wwwcont/mpei-mps-kp/А-09-23/3 Друговская Е.М./СХЕМА-1/perechen.pdf

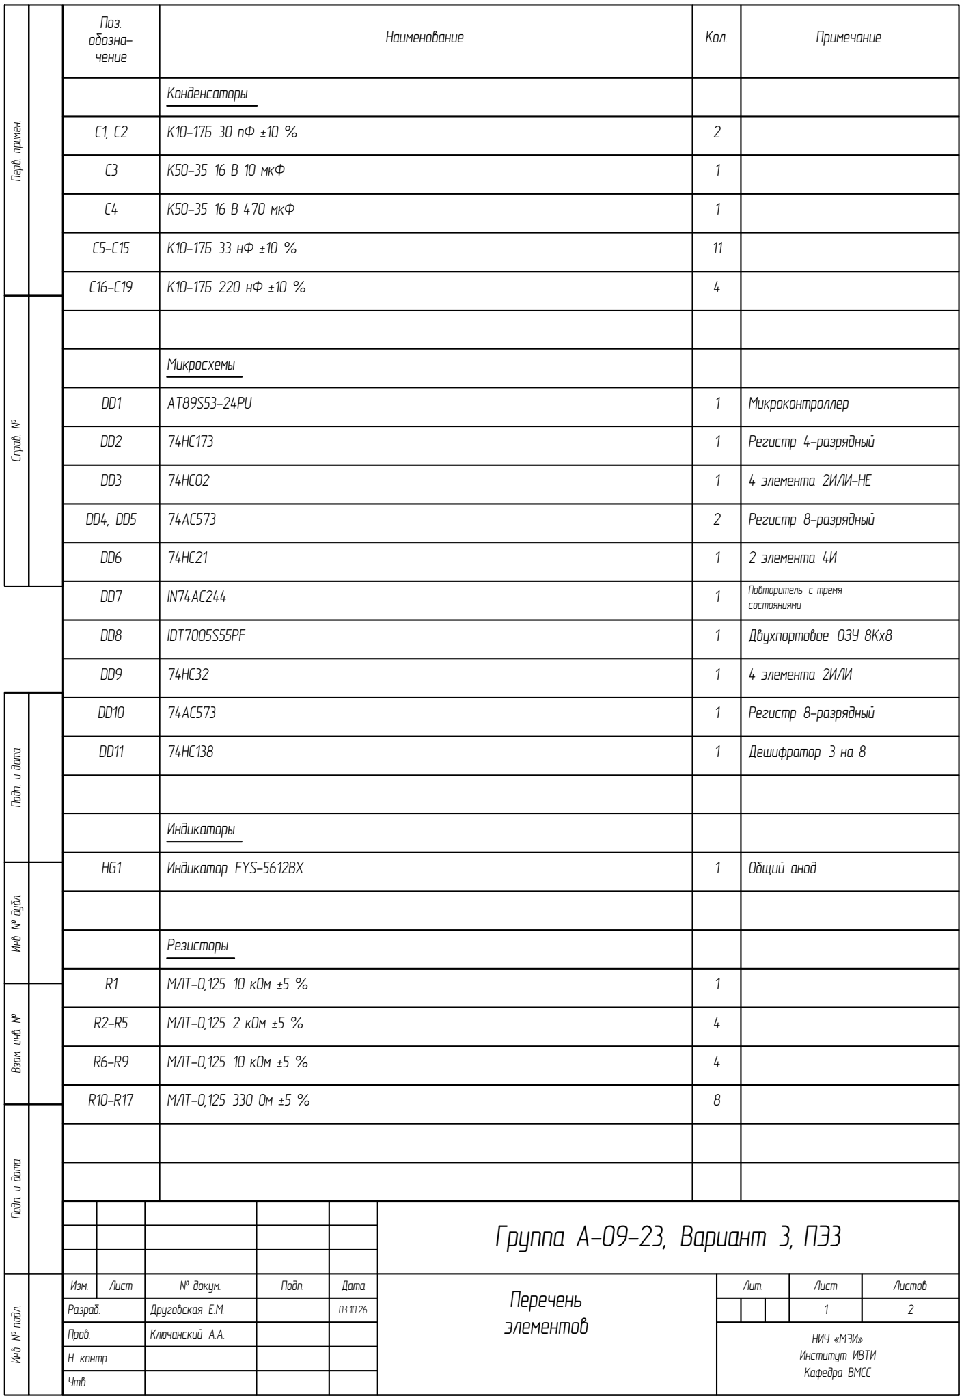
[picture p52: figure]
Изм.; Лист; № докум.; Подп.; Дата; Разраб.; Пров.; Н. контр.; Утв.; Друговская Е.М.; Перечень элементов; Лит.; Листов; НИУ «МЭИ» Институт ИВТИ; Микроконтроллер; IDT7005S55PF; Общий анод; МЛТ-0,125 330 Ом ±5 %; Резисторы; МЛТ-0,125 2 кОм ±5 %; МЛТ-0,125 10 кОм ±5 %; Индикатор FYS-5612BX; Индикаторы; Поз.; Двухпортовое ОЗУ 8Кx8; состояниями 1; 2 элемента 4И; Кол.; Примечание; 4 элемента 2ИЛИ; Наименование; Конденсаторы; обозна- чение; Регистр 8-разрядный; 4 элемента 2ИЛИ-НЕ; Регистр 4-разрядный; Микросхемы; К50-35 16 В 10 мкФ; К50-35 16 В 470 мкФ; Дешифратор 3 на 8; Повторитель с тремя

Ключанский А.А. | 03.10.26 | Группа А-09-23, Вариант 3, ПЭ3

Кафедра ВМСС Инв. № подл. Подп. и дата Взам. инв.

№ Инв. № дубл. Подп. и дата Перв. примен. Справ.

Изм. | Лист | № докум. | Подп. | Дата | Группа А-09-23, Вариант 3, ПЭ3

Лист

2 Инв. № подл. Подп. и дата Взам. инв.

№ Инв. № дубл. Подп. и дата

Диод КД521А

XS1

VD1–VD3

Диоды

Разъёмы

3

Розетка PBS-23

ZQ1 | 1

Резонаторы

Резонатор кварцевый HC-49S 12 МГц

обозна- | Наименование | Кол. | Примечание
чение
1 | 23 конт.
SB1–SB12 | Кнопка DTSM-62N-V | 12
| Кнопки

Поз.
