wwwcont/mpei-mps-kp/А-12-23/14 Студентов С.С./СХЕМА-1/perechen.pdf

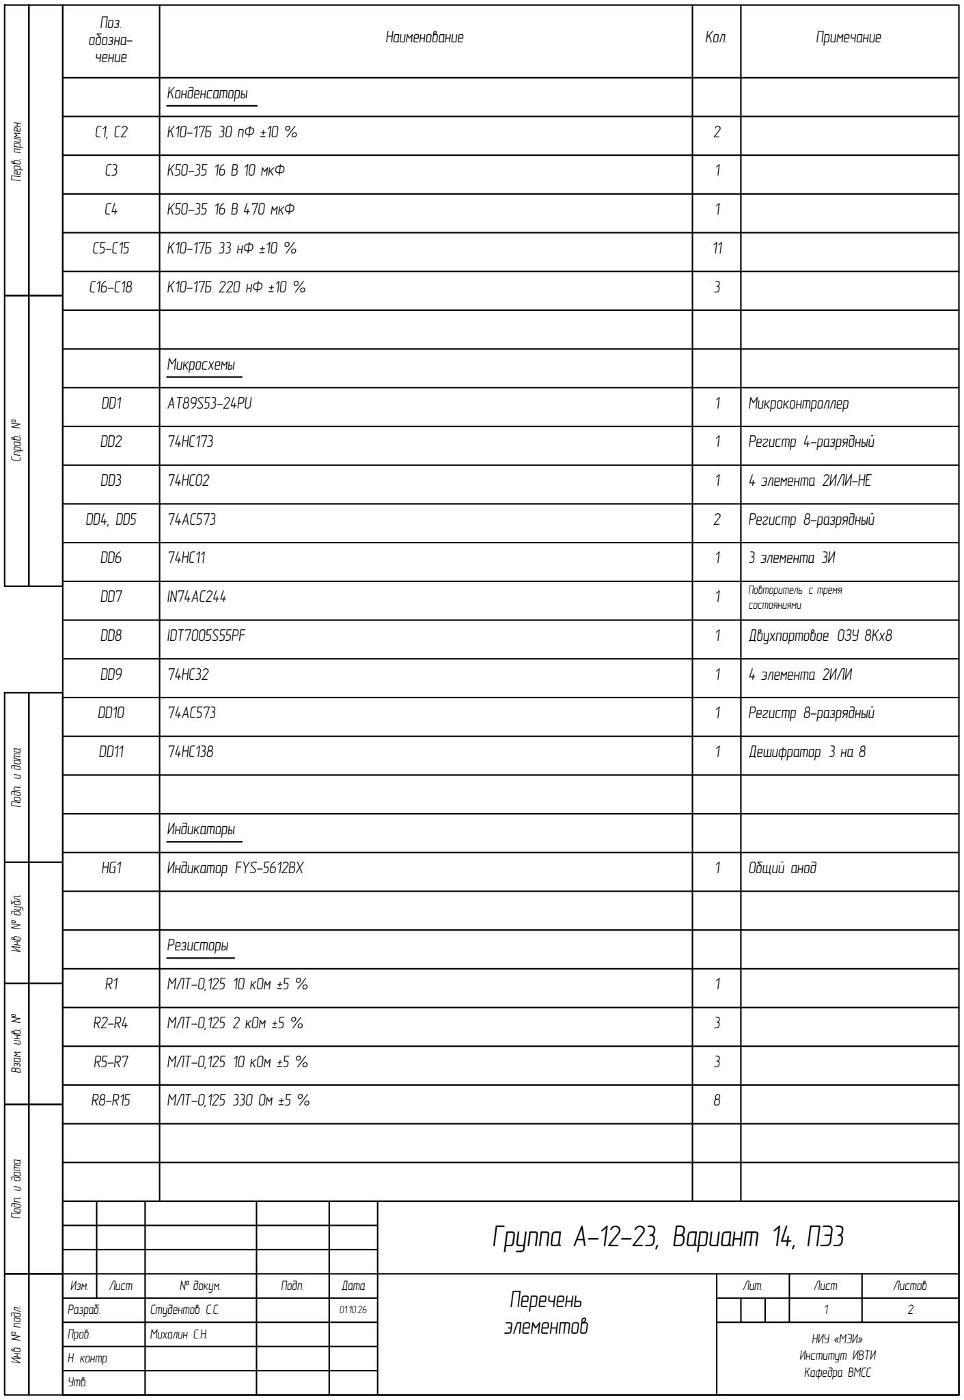
[picture p53: figure]
Изм.; Лист; № докум.; Подп.; Дата; Разраб.; Пров.; Н. контр.; Утв.; Студентов С.С.; Перечень элементов; Лит.; Листов; НИУ «МЭИ» Институт ИВТИ; Микроконтроллер; IDT7005S55PF; Общий анод; МЛТ-0,125 330 Ом ±5 %; Резисторы; МЛТ-0,125 2 кОм ±5 %; МЛТ-0,125 10 кОм ±5 %; Индикатор FYS-5612BX; Индикаторы; Поз.; Двухпортовое ОЗУ 8Кx8; состояниями 1; 3 элемента 3И; Кол.; Примечание; 4 элемента 2ИЛИ; Наименование; Конденсаторы; обозна- чение; Регистр 8-разрядный; 4 элемента 2ИЛИ-НЕ; Регистр 4-разрядный; Микросхемы; К50-35 16 В 10 мкФ; К50-35 16 В 470 мкФ; Дешифратор 3 на 8; Повторитель с тремя

Михалин С.Н. | 01.10.26 | Группа А-12-23, Вариант 14, ПЭ3

Кафедра ВМСС Инв. № подл. Подп. и дата Взам. инв.

№ Инв. № дубл. Подп. и дата Перв. примен. Справ.

Изм. | Лист | № докум. | Подп. | Дата | Группа А-12-23, Вариант 14, ПЭ3

Лист

2 Инв. № подл. Подп. и дата Взам. инв.

№ Инв. № дубл. Подп. и дата

XS1

XS3

XS2 | Розетка PBS-10
| Розетка PBS-11

1

Розетка PBS-2 | 2 конт.

Резонатор кварцевый HC-49S 12 МГц

1

Резонаторы

ZQ1

Наименование

Кнопки

SB1–SB12 | Кнопка DTSM-62N-V | 12
VD1–VD4 | Диод КД521А | 4

чение

обозна-

11 конт.

Кол. | Примечание

Поз.

Диоды

Разъёмы

10 конт.

1

1
