wwwcont/mpei-mps-kp/students/a06_groshev_av/pz/pz1.md

<!-- Текст студента для ПЗ1. Каждый раздел начинается строкой «## ид — название»: ид не менять.
     Строки «> ✍ …» — подсказки, в документ не попадают. Пиши под подсказкой обычными абзацами;
     markdown можно: **жирный**, *курсив*, списки через «- ». Пустой раздел → в документе жёлтое «ДОПИШИ».
     Файл можно пересоздать (make pz-init): написанный текст сохранится. -->

## p1.intro — Введение: своими словами
> ✍ одним абзацем — что делает твоя система и чем вариант отличается (клавиатура, индикатор, сигналы Y). Можно удалить подсказку, если введение устраивает.

Проектируемая система на AT89S53 собирает отсчёты X2, которые присылает внешнее устройство, в кольцевой буфер на двухпортовом ОЗУ IDT7005, а по ним и по числу X1, набранному оператором, вырабатывает выходной код Y2 = (7 + X1 + X2) mod 256 со стробом на P1.2. В моём варианте (А-06, M = 1) клавиатура 3×4 — три столбца и четыре строки, нажатие сообщается прерыванием INT0; введённая цифра выводится на семисегментный индикатор с общим катодом и гаснет через T3 = 2150 мс. Клавиша «Тест» запускает строб Y1 длительностью 176 мс на выводе P1.1, а буфер рассчитан на 1210 байт (адреса 2000h–24B9h). Все внешние устройства выбираются дешифратором 74HC138 по старшим линиям адреса A13–A15, пока CS_EN = P3.4 равен 1.

## p1.buffer — Механизм обмена через буфер
> ✍ опиши своими словами, как внешнее устройство записывает X2 и как МК читает буфер (кто выставляет адрес, какой строб, какое прерывание, кто двигает «голову» и «хвост»). 3–5 предложений.

Порты IDT7005 в моей схеме разделены между двумя хозяевами. Правый порт целиком выведен на отдельный разъём доступа к буферу: внешнее устройство само выставляет адрес A0R–A12R, данные I/O0R–I/O7R и строб на R/WR (CER постоянно на земле, OER — на +5 В) и записывает очередной отсчёт X2 в ячейку обмена 3FFFh, которая лежит за пределами кольца 2000h–24B9h. Тот же строб заведён на INT1 (P3.3): прерывание срабатывает по спаду, но ОЗУ фиксирует байт только по фронту, поэтому обработчик сначала дожидается, пока P3.3 вернётся в 1, и лишь затем читает 3FFFh. Левый порт полностью принадлежит МК — адрес A0–A12, данные D0–D7, CE от выхода Y1 дешифратора, OE от RD, R/W от WR, — так что через него программа и забирает байт из ячейки обмена, и пишет его в кольцо командой movx @DPTR,A по адресу «головы». Указатели «голова» и «хвост», а также флаги пустоты и переполнения хранятся во внутреннем ОЗУ и меняются только программой: «голову» сдвигает процедура записи, вызванная из обработчика INT1, «хвост» — процедура чтения в основном цикле. Прочитанный по «хвосту» отсчёт основная программа использует для расчёта Y2 = (7 + X1 + X2) mod 256 и выдаёт его со стробом на P1.2.

## p1.timing — Вывод по временам IDT7005
> ✍ свой вывод по сравнению времён (2–4 предложения) (необязательно: без текста в документ идёт пересказ схемы)
