wwwcont/mpei-mps-kp/students/a06_groshev_av/pz/pz2.md

<!-- Текст студента для ПЗ2. Каждый раздел начинается строкой «## ид — название»: ид не менять.
     Строки «> ✍ …» — подсказки, в документ не попадают. Пиши под подсказкой обычными абзацами;
     markdown можно: **жирный**, *курсив*, списки через «- ». Пустой раздел → в документе жёлтое «ДОПИШИ».
     Файл можно пересоздать (make pz-init): написанный текст сохранится. -->

## p2.ide — Среда разработки и компилятор
> ✍ если работали в другой среде — впишите свою (название и версия, например «MCU 8051 IDE 1.4.9») (необязательно: без текста в документ идёт пересказ схемы)

## p2.alg — Алгоритм программы в целом
> ✍ опиши основной цикл: что делается после сброса (инициализация), что крутится в основном цикле и какие действия выполняются в прерываниях (клавиатура — INT0, X2 — INT1, таймеры). 1–2 абзаца, со ссылками на рисунки ниже.

После сброса МК выполняет инициализацию (рисунок 1): ставит стек на 07h, разрешает дешифратор адреса (CS_EN = 1), переводит стробы Y1 и Y2 в пассивную единицу, опускает все столбцы клавиатуры и гасит индикатор, объявляет буфер пустым, настраивает Timer0 и Timer1 в режим 1, а INT0 и INT1 — на срабатывание по спаду, и только после этого разрешает прерывания. Основная программа (рисунок 2) в цикле смотрит, есть ли что выдавать: если X1 ≠ 0, в буфере есть отсчёт и предыдущий строб Y2 уже закончился, она читает отсчёт из «хвоста» и выдаёт Y2 = (7 + X1 + X2) mod 256 со стробом.

Всё, что связано со временем и с внешними событиями, сделано в прерываниях. INT0 приходит от клавиатуры: обработчик опрашивает матрицу (рисунок 3) и по коду клавиши меняет X1, запускает строб Y1 или очищает буфер (рисунок 4). INT1 — строб внешнего устройства, которым оно уже записало X2 в ячейку обмена 3FFFh через правый порт: обработчик ждёт, пока строб закончится, забирает байт из этой ячейки и кладёт его в кольцо по адресу «головы» (рисунки 5 и 6). Timer0 тикает каждые 2 мс и отсчитывает длительность строба Y1 и время индикации T3 (рисунок 10), Timer1 одним интервалом отмеряет строб Y2 1536 мкс и поднимает его (рисунок 13). Благодаря этому ни одна процедура не ждёт в цикле, и основная программа всегда готова обработать следующий отсчёт.

## flow.01-init — Пояснение к рисунку 1
> ✍ своё пояснение к рисунку 1 («Инициализация МПС и основная программа»): что делает алгоритм по шагам и почему так (3–6 предложений) (необязательно: без текста в документ идёт пересказ схемы)

## flow.02-main — Пояснение к рисунку 2
> ✍ своё пояснение к рисунку 2 («Основной цикл программы»): что делает алгоритм по шагам и почему так (3–6 предложений) (необязательно: без текста в документ идёт пересказ схемы)

## flow.03-kbscan — Пояснение к рисунку 3
> ✍ своё пояснение к рисунку 3 («Опрос клавиатуры (обработчик INT0)»): что делает алгоритм по шагам и почему так (3–6 предложений) (необязательно: без текста в документ идёт пересказ схемы)

Процедура KbScan по очереди опускает в 0 один из трёх столбцов и читает четыре строки. Старшие биты прочитанного байта не подключены, поэтому они отбрасываются маской, а оставшиеся биты инвертируются, чтобы замкнутая строка давала 1. Каждая найденная единица увеличивает счётчик нажатий, а индекс клавиши считается как номер столбца плюс три на каждую строку вниз — это сразу номер элемента в таблице KeyTab. После опроса все столбцы снова опускаются, иначе следующее нажатие не вызовет INT0, и сбрасывается IE0, который успел установиться, пока линия дёргалась при переборе столбцов. Код из таблицы возвращается, только если нажата ровно одна клавиша; иначе возвращается FFh.

## flow.04-keys — Пояснение к рисунку 4
> ✍ своё пояснение к рисунку 4 («Обработчик прерывания INT0: реакция на клавишу»): что делает алгоритм по шагам и почему так (3–6 предложений) (необязательно: без текста в документ идёт пересказ схемы)

## flow.05-bufwrite — Пояснение к рисунку 5
> ✍ своё пояснение к рисунку 5 («Запись отсчёта в кольцевой буфер»): что делает алгоритм по шагам и почему так (3–6 предложений) (необязательно: без текста в документ идёт пересказ схемы)

BufWrite сначала проверяет, полон ли буфер: это случай, когда буфер не пуст, а «голова» совпала с «хвостом» по обоим байтам адреса. Тогда самый старый отсчёт приносится в жертву — «хвост» сдвигается на одну ячейку, и ставится флаг переполнения. Затем отсчёт записывается по адресу «головы», «голова» переходит к следующей ячейке через общую подпрограмму NextCell (после 24B9h она возвращается на 2000h), а флаг пустоты сбрасывается. Так в буфере всегда помещается V = 1210 отсчётов, и при переполнении теряются самые давние данные, а не только что пришедшие.

## flow.05a-x2isr — Пояснение к рисунку 6
> ✍ своё пояснение к рисунку 6 («Обработчик прерывания INT1: приём отсчёта X2 от внешнего устройства»): что делает алгоритм по шагам и почему так (3–6 предложений) (необязательно: без текста в документ идёт пересказ схемы)

К моменту входа в обработчик внешнее устройство уже выставило отсчёт на правый порт IDT7005 и держит строб в нуле, но сама запись в ячейку обмена 3FFFh завершается только по фронту строба. Поэтому после сохранения A, PSW и DPTR обработчик крутится на проверке P3.3 и выходит из ожидания, когда строб вернулся в 1. Затем по адресу 3FFFh командой movx A,@DPTR через левый порт читается принятый байт и передаётся в BufWrite, которая кладёт его в кольцо и сдвигает «голову». В конце регистры восстанавливаются в обратном порядке. Ожидание короткое — оно длится не дольше самого строба, — а без него МК мог бы прочитать из ячейки обмена ещё прошлый отсчёт.

## flow.06-bufread — Пояснение к рисунку 7
> ✍ своё пояснение к рисунку 7 («Чтение отсчёта из кольцевого буфера»): что делает алгоритм по шагам и почему так (3–6 предложений) (необязательно: без текста в документ идёт пересказ схемы)

## flow.07-bufclear — Пояснение к рисунку 8
> ✍ своё пояснение к рисунку 8 («Очистка кольцевого буфера (клавиша «Сброс»)»): что делает алгоритм по шагам и почему так (3–6 предложений) (необязательно: без текста в документ идёт пересказ схемы)

## flow.08-show — Пояснение к рисунку 9
> ✍ своё пояснение к рисунку 9 («Вывод символа на индикатор»): что делает алгоритм по шагам и почему так (3–6 предложений) (необязательно: без текста в документ идёт пересказ схемы)

## flow.09-t0 — Пояснение к рисунку 10
> ✍ своё пояснение к рисунку 10 («Обработчик прерывания Timer0: отсчёт T1 и T3»): что делает алгоритм по шагам и почему так (3–6 предложений) (необязательно: без текста в документ идёт пересказ схемы)

Timer0 работает в 16-разрядном режиме и переполняется каждые 2 мс. В обработчике таймер на несколько тактов останавливается, и к тому, что он успел насчитать после переполнения, прибавляется F830h плюс семь тактов остановки — так задержка входа в прерывание не накапливается, и за 88 тиков строб получается 176 мс без заметной ошибки. После перезапуска уменьшается счётчик тиков; когда он доходит до нуля, таймер останавливается и строб Y1 поднимается в 1. A и PSW сохраняются в стеке, потому что прерывание может прийти в любом месте основной программы.

## flow.10-y1 — Пояснение к рисунку 11
> ✍ своё пояснение к рисунку 11 («Начало строба Y1»): что делает алгоритм по шагам и почему так (3–6 предложений) (необязательно: без текста в документ идёт пересказ схемы)

Y1Start не ждёт окончания строба, а только запускает его. Сначала Timer0 останавливается, чтобы повторное нажатие «Тест» начинало отсчёт заново, затем в таймер загружается первый тик 2 мс, а счётчик тиков ставится на 88. После этого вывод P1.1 опускается в 0 и таймер запускается; дальше длительность отсчитывает обработчик Timer0, а процедура сразу возвращается.

## flow.11-y2 — Пояснение к рисунку 12
> ✍ своё пояснение к рисунку 12 («Расчёт и выдача сигнала Y2»): что делает алгоритм по шагам и почему так (3–6 предложений) (необязательно: без текста в документ идёт пересказ схемы)

## flow.12-t1 — Пояснение к рисунку 13
> ✍ своё пояснение к рисунку 13 («Обработчик прерывания Timer1: конец строба Y2»): что делает алгоритм по шагам и почему так (3–6 предложений) (необязательно: без текста в документ идёт пересказ схемы)

## p2.errors — Коды ошибок
> ✍ проверь таблицу кодов ошибок выше: оставь те, что обрабатывает твоя программа, и одним-двумя предложениями опиши реакцию на ошибку (или напиши «таблица соответствует программе»).

Таблица описывает реакцию системы в целом. В моих программах ошибки «1.» и «2.» процедура опроса KbScan не различает — в обоих случаях она возвращает FFh, и обработчик клавиш выводит код ошибки; признаком ошибки «3.» служит флаг переполнения, который ставит BufWrite, когда новый отсчёт затирает непрочитанный, а «4.» относится к повторному нажатию «Тест» во время строба Y1 (в Y1Start такой вызов просто перезапускает отсчёт T1). Ошибка только показывается на индикаторе с точкой dp; указатели буфера, X1 и выходы Y1, Y2 при этом не меняются.
