wwwcont/mpei-mps-kp/students/a08_laptashkin_vi/pz/pz1.md

<!-- Текст студента для ПЗ1. Каждый раздел начинается строкой «## ид — название»: ид не менять.
     Строки «> ✍ …» — подсказки, в документ не попадают. Пиши под подсказкой обычными абзацами;
     markdown можно: **жирный**, *курсив*, списки через «- ». Пустой раздел → в документе жёлтое «ДОПИШИ».
     Файл можно пересоздать (make pz-init): написанный текст сохранится. -->

## p1.intro — Введение: своими словами
> ✍ одним абзацем — что делает твоя система и чем вариант отличается (клавиатура, индикатор, сигналы Y). Можно удалить подсказку, если введение устраивает.

В работе проектируется аппаратная часть микропроцессорной системы на AT89S53 для варианта 12 группы А-08. Система собирает отсчёты сигнала X2 от внешнего устройства в кольцевой буфер на 1528 байт (двухпортовое ОЗУ IDT7005, ячейки 6000h–65F7h), принимает команды и число X1 с клавиатуры 4×3, показывает символ на семисегментном индикаторе с общим анодом и формирует выходные сигналы: строб Y1 длительностью 298 мс на выводе P1.5 и байт Y2 = (20 + X1 + X2) mod 256, который заносится в отдельный регистр и сопровождается стробом 2068 мкс на P1.6. Особенность задания этого года — все внешние устройства выбираются через дешифратор 74HC138 по старшим разрядам адреса A13–A15 (у меня буфер — выход Y3, регистр Y2 — Y4, индикатор — Y5, клавиатура — Y6), а сам дешифратор включается линией CS_EN = P3.4.

## p1.buffer — Механизм обмена через буфер
> ✍ опиши своими словами, как внешнее устройство записывает X2 и как МК читает буфер (кто выставляет адрес, какой строб, какое прерывание, кто двигает «голову» и «хвост»). 3–5 предложений.

У IDT7005 два полностью независимых порта, и каждый подключён к своему хозяину. Левый порт целиком принадлежит микроконтроллеру: на него идут адрес A0–A12 с шины, данные D0–D7, выбор CS_buf (выход Y3 дешифратора), OE от RD и R/W от WR, поэтому через него МК и записывает отсчёты в кольцо 6000h–65F7h, и читает их обратно. Правый порт выведен на отдельный разъём: внешнее устройство само выставляет адрес 7FFFh (ячейка обмена за пределами кольца) и байт X2, а своим стробом X2 на R/WR записывает его в ОЗУ; CER у правого порта постоянно на земле, OER — на +5 В. Тот же строб заведён на INT1, и прерывание приходит по его спаду, тогда как байт фиксируется в ячейке только по фронту, поэтому обработчик сначала ждёт, пока P3.3 вернётся в 1, и лишь потом читает ячейку 7FFFh через левый порт. Прочитанный отсчёт МК кладёт по адресу «головы» процедурой записи в буфер, сдвигает «голову» и ведёт флаги пустоты и переполнения — внешнее устройство об указателях ничего не знает. Когда отсчёт нужен для расчёта Y2, МК читает ячейку «хвоста» командой movx A, @DPTR, сдвигает «хвост» (на границе 65F7h оба указателя заворачиваются на 6000h) и пересчитанный байт заносит в регистр Y2.

## p1.timing — Вывод по временам IDT7005
> ✍ свой вывод по сравнению времён (2–4 предложения) (необязательно: без текста в документ идёт пересказ схемы)

Из таблицы видно, что самое жёсткое требование ОЗУ — выдать данные не позже 55 нс после установки адреса, а МК при кварце 12 МГц ждёт их почти 500 нс, то есть микросхема успевает с большим запасом. При записи в кольцо импульс WR длится не меньше 400 нс против нужных IDT7005 40 нс, а данные на P0 держатся всё это время, так что запись левым портом тоже проходит надёжно. Правый порт от МК не зависит: его времена должно выдерживать внешнее устройство на разъёме. Значит, буфер можно подключать прямо к шине P0/P2 без дополнительных задержек и согласующих элементов.
