wwwcont/mpei-mps-kp/students/a08_laptashkin_vi/pz/pz2.md

<!-- Текст студента для ПЗ2. Каждый раздел начинается строкой «## ид — название»: ид не менять.
     Строки «> ✍ …» — подсказки, в документ не попадают. Пиши под подсказкой обычными абзацами;
     markdown можно: **жирный**, *курсив*, списки через «- ». Пустой раздел → в документе жёлтое «ДОПИШИ».
     Файл можно пересоздать (make pz-init): написанный текст сохранится. -->

## p2.ide — Среда разработки и компилятор
> ✍ если работали в другой среде — впишите свою (название и версия, например «MCU 8051 IDE 1.4.9») (необязательно: без текста в документ идёт пересказ схемы)

## p2.alg — Алгоритм программы в целом
> ✍ опиши основной цикл: что делается после сброса (инициализация), что крутится в основном цикле и какие действия выполняются в прерываниях (клавиатура — INT0, X2 — INT1, таймеры). 1–2 абзаца, со ссылками на рисунки ниже.

После сброса МПС выполняет инициализацию (рисунок 3.1): ставит стек на 07h, включает дешифратор адреса линией CS_EN, опускает все столбцы клавиатуры, гасит индикатор, задаёт режимы таймеров и разрешает прерывания. Дальше всю срочную работу делают обработчики: INT0 срабатывает по нажатию клавиши и вызывает опрос матрицы, INT1 по стробу X2 дожидается конца строба, забирает из ячейки обмена отсчёт, который внешнее устройство записало туда правым портом IDT7005, и кладёт его в кольцевой буфер, Timer0 отсчитывает длительности T1 (строб Y1) и T3 (время показа символа), а Timer1 — длительность строба Y2.

Основной цикл (рисунок 3.2) только следит за условием выдачи Y2: если X1 ≠ 0, в буфере есть отсчёты и предыдущий строб Y2 закончился, он забирает отсчёт из буфера, считает Y2 = (20 + X1 + X2) mod 256 и выдаёт его со стробом; при X1 = 0 в регистр один раз записывается ноль. Три программы для робота — это отдельные куски этой системы: обработчик клавиатуры (рисунок 3.3), чтение из буфера (рисунок 3.7) и вывод символа с гашением по T3 (рисунки 3.9 и 3.10); в них сделана только своя часть инициализации, остальное время МК стоит на команде jmp $.

## flow.01-init — Пояснение к рисунку 3.1
> ✍ своё пояснение к рисунку 3.1 («Инициализация МПС и основная программа»): что делает алгоритм по шагам и почему так (3–6 предложений) (необязательно: без текста в документ идёт пересказ схемы)

Сначала задаётся SP = 07h, чтобы стек лежал сразу за банком регистров 0, и ставится CS_EN = 1 — без этого дешифратор 74HC138 не выдаст ни одного CS и команды movx никуда не попадут. Затем переменные получают начальные значения: буфер пуст (голова = хвост = 6000h, F_EMPTY = 1), X1 = 0, стробы Y1 и Y2 в единице. В регистр столбцов пишется 0, чтобы любое нажатие сразу опустило строку и дало спад на INT0, а индикатор гасится кодом FFh. Последними настраиваются таймеры и разрешаются прерывания: если разрешить их раньше, обработчик мог бы застать недонастроенные переменные.

## flow.02-main — Пояснение к рисунку 3.2
> ✍ своё пояснение к рисунку 3.2 («Основной цикл программы»): что делает алгоритм по шагам и почему так (3–6 предложений) (необязательно: без текста в документ идёт пересказ схемы)

## flow.03-kbscan — Пояснение к рисунку 3.3
> ✍ своё пояснение к рисунку 3.3 («Опрос клавиатуры (обработчик INT0)»): что делает алгоритм по шагам и почему так (3–6 предложений) (необязательно: без текста в документ идёт пересказ схемы)

Опрос идёт по столбцам: маска с одним нулём записывается в регистр столбцов, и из ячейки клавиатуры читаются три младших бита — состояние строк, старшие биты шины отбрасываются. Внутри столбца строки перебираются сдвигом через перенос, номер клавиши при переходе на строку ниже увеличивается на 4 (число столбцов). Я не останавливаюсь на первом найденном контакте, а считаю все замыкания: только если за весь опрос нашлось ровно одно, номер клавиши переводится в код по таблице KbCodes, иначе (помеха или две клавиши сразу) возвращается FFh. В конце все столбцы снова опускаются в 0, а IE0 сбрасывается — пока перебирались столбцы, линия INT0 дёргалась, и без сброса обработчик вызвался бы ещё раз.

## flow.04-keys — Пояснение к рисунку 3.4
> ✍ своё пояснение к рисунку 3.4 («Обработчик прерывания INT0: реакция на клавишу»): что делает алгоритм по шагам и почему так (3–6 предложений) (необязательно: без текста в документ идёт пересказ схемы)

## flow.05-bufwrite — Пояснение к рисунку 3.5
> ✍ своё пояснение к рисунку 3.5 («Запись отсчёта в кольцевой буфер»): что делает алгоритм по шагам и почему так (3–6 предложений) (необязательно: без текста в документ идёт пересказ схемы)

## flow.05a-x2isr — Пояснение к рисунку 3.6
> ✍ своё пояснение к рисунку 3.6 («Обработчик прерывания INT1: приём отсчёта X2 от внешнего устройства»): что делает алгоритм по шагам и почему так (3–6 предложений) (необязательно: без текста в документ идёт пересказ схемы)

К моменту прерывания отсчёт X2 уже пишется внешним устройством через правый порт IDT7005 в ячейку обмена 7FFFh — МК в этой записи не участвует. Обработчик сохраняет A, PSW и DPTR, потому что вызывается посреди любой другой работы. Затем он крутится на проверке P3.3: INT1 настроен на спад строба, а в ОЗУ байт защёлкивается только по фронту, и если читать сразу, можно получить старое содержимое ячейки. Когда строб закончился, ячейка 7FFFh читается левым портом командой movx A, @DPTR, и отсчёт передаётся процедуре записи в кольцо (рисунок 3.5), которая сама сдвигает «голову» и ставит флаги. В конце регистры восстанавливаются в обратном порядке.

## flow.06-bufread — Пояснение к рисунку 3.7
> ✍ своё пояснение к рисунку 3.7 («Чтение отсчёта из кольцевого буфера»): что делает алгоритм по шагам и почему так (3–6 предложений) (необязательно: без текста в документ идёт пересказ схемы)

Сначала проверяется флаг пустоты: если читать нечего, процедура сразу возвращает 0 и не трогает ни указатели, ни флаги. Иначе адрес «хвоста» загружается в DPTR, байт читается через левый порт IDT7005 и откладывается в B, потому что аккумулятор нужен для сравнений. «Хвост» увеличивается на единицу, и если он дошёл до BUF_END = 65F8h (сравниваются оба байта адреса), то возвращается на начало 6000h. После чтения одна ячейка заведомо свободна, поэтому флаг переполнения сбрасывается, а если «хвост» догнал «голову», ставится флаг пустоты.

## flow.07-bufclear — Пояснение к рисунку 3.8
> ✍ своё пояснение к рисунку 3.8 («Очистка кольцевого буфера (клавиша «Сброс»)»): что делает алгоритм по шагам и почему так (3–6 предложений) (необязательно: без текста в документ идёт пересказ схемы)

## flow.08-show — Пояснение к рисунку 3.9
> ✍ своё пояснение к рисунку 3.9 («Вывод символа на индикатор»): что делает алгоритм по шагам и почему так (3–6 предложений) (необязательно: без текста в документ идёт пересказ схемы)

Процедура сначала останавливает Timer0 и сбрасывает TF0: если предыдущий символ ещё показывается, его отсчёт T3 прерывается и начинается заново. Код больше 10 означает «погасить» — в регистр индикатора сразу пишется FFh, и таймер не запускается. Для кодов 0–10 сегменты берутся из таблицы SegTab, составленной для общего катода, и инвертируются командой xrl A, #IND_OFF, так как у моего индикатора общий анод и сегмент горит при нуле. После записи символа задаётся счёт тиков T3 (1410 по 2 мс) и запускается Timer0; процедура возвращается сразу, ожидание идёт в прерываниях.

## flow.09-t0 — Пояснение к рисунку 3.10
> ✍ своё пояснение к рисунку 3.10 («Обработчик прерывания Timer0: отсчёт T1 и T3»): что делает алгоритм по шагам и почему так (3–6 предложений) (необязательно: без текста в документ идёт пересказ схемы)

Timer0 работает в режиме 2 (8 бит с автоперезагрузкой): переполнение приходит каждые 200 мкс, и перезагружать таймер программно не нужно, поэтому задержка входа в прерывание не копится в длительности. Десять переполнений образуют тик 2 мс, на каждом тике уменьшается двухбайтовый счётчик тиков (младший байт гоняется командой djnz, старший — после каждого его круга). Когда тики кончились, таймер останавливается и в зависимости от того, что отсчитывалось, либо снимается строб Y1, либо гасится индикатор. Команды djnz не меняют флаги, поэтому PSW сохранять не нужно, а A и DPTR кладутся в стек только в ветке гашения, где они реально используются; в программе 3 используется только ветка T3.

## flow.10-y1 — Пояснение к рисунку 3.11
> ✍ своё пояснение к рисунку 3.11 («Начало строба Y1»): что делает алгоритм по шагам и почему так (3–6 предложений) (необязательно: без текста в документ идёт пересказ схемы)

## flow.11-y2 — Пояснение к рисунку 3.12
> ✍ своё пояснение к рисунку 3.12 («Расчёт и выдача сигнала Y2»): что делает алгоритм по шагам и почему так (3–6 предложений) (необязательно: без текста в документ идёт пересказ схемы)

## flow.12-t1 — Пояснение к рисунку 3.13
> ✍ своё пояснение к рисунку 3.13 («Обработчик прерывания Timer1: конец строба Y2»): что делает алгоритм по шагам и почему так (3–6 предложений) (необязательно: без текста в документ идёт пересказ схемы)

## p2.errors — Коды ошибок
> ✍ проверь таблицу кодов ошибок выше: оставь те, что обрабатывает твоя программа, и одним-двумя предложениями опиши реакцию на ошибку (или напиши «таблица соответствует программе»).

Таблица описывает реакцию полной системы. В сданных программах из неё реализовано распознавание ошибок клавиатуры: если при опросе замкнуто больше одного контакта или прерывание пришло без нажатия, процедура KbScan возвращает FFh вместо кода клавиши, и вместо цифры на индикатор выводится код ошибки с горящей точкой. Оба случая дают в A одно и то же FFh; различить «1.» и «2.» можно по числу найденных замыканий (больше одного или ни одного), которое процедура считает во время опроса. Переполнение буфера («3.») отмечается флагом F_OVF, который снимает процедура чтения; «4.» выводится, если «Тест» нажат во время строба Y1. Индикация ошибки держится до нажатия любой клавиши, но не дольше T3.
