wwwcont/mpei-mps-kp/students/a09_drugovskaya_em/pz/pz1.md

<!-- Текст студента для ПЗ1. Каждый раздел начинается строкой «## ид — название»: ид не менять.
     Строки «> ✍ …» — подсказки, в документ не попадают. Пиши под подсказкой обычными абзацами;
     markdown можно: **жирный**, *курсив*, списки через «- ». Пустой раздел → в документе жёлтое «ДОПИШИ».
     Файл можно пересоздать (make pz-init): написанный текст сохранится. -->

## p1.intro — Введение: своими словами
> ✍ одним абзацем — что делает твоя система и чем вариант отличается (клавиатура, индикатор, сигналы Y). Можно удалить подсказку, если введение устраивает.

Разрабатываемая система собрана на микроконтроллере AT89S53: она принимает поток отсчётов X2 от внешнего устройства, накапливает их в кольцевом буфере на двухпортовом ОЗУ IDT7005 и по каждому отсчёту выдаёт результат Y2 = (12 + X1 + X2) mod 256 в выходной регистр со стробом. Число X1 оператор набирает на клавиатуре 3×4 (три столбца, четыре строки — нечётный вариант), введённый символ на время T3 = 2430 мс показывается на семисегментном индикаторе с общим анодом. Клавиша «Тест» запускает строб Y1 длительностью 215 мс на выводе P1.3, строб Y2 длительностью 1899 мкс выдаётся на P1.4. Внешние устройства выбираются дешифратором 74HC138 по старшим линиям адреса: буфер — выходом Y4, индикатор — Y5, регистр Y2 — Y6, клавиатура — Y7.

## p1.buffer — Механизм обмена через буфер
> ✍ опиши своими словами, как внешнее устройство записывает X2 и как МК читает буфер (кто выставляет адрес, какой строб, какое прерывание, кто двигает «голову» и «хвост»). 3–5 предложений.

Отсчёт X2 попадает в микроконтроллер в два этапа. Сначала внешнее устройство через отдельный разъём доступа к буферу само выставляет на правом порту IDT7005 адрес ячейки обмена 9FFFh (последняя ячейка окна буфера, вне кольца) и байт X2 и даёт строб записи — микроконтроллер в этом не участвует. Тот же строб заведён на вход INT1 (P3.3): прерывание срабатывает по спаду, а ОЗУ фиксирует байт по фронту, поэтому обработчик сначала дожидается, пока P3.3 вернётся в единицу, и только потом читает ячейку 9FFFh через левый порт. Прочитанный отсчёт процедура записи кладёт в кольцо 8000h–85F9h (1530 байт) по адресу «головы» и сдвигает её; если кольцо уже заполнено, вперёд уходит и «хвост», самый старый отсчёт теряется и ставится флаг переполнения. Основная программа забирает отсчёты по «хвосту» тем же левым портом и по ним вычисляет и выдаёт Y2. «Голова», «хвост» и флаги пустоты и переполнения хранятся во внутренней памяти микроконтроллера (44h–47h, биты 20h.3 и 21h.4), и меняет их только программа.

## p1.timing — Вывод по временам IDT7005
> ✍ свой вывод по сравнению времён (2–4 предложения) (необязательно: без текста в документ идёт пересказ схемы)

По таблице сравнения видно, что IDT7005 намного быстрее, чем требует шина AT89S53 при кварце 12 МГц: памяти нужно 55 нс от адреса до данных и 40 нс на импульс записи, а микроконтроллер отводит на это около 500 и 400 нс. Поэтому буфер подключается к шине напрямую, без тактов ожидания, а запас в сотни наносекунд с избытком покрывает задержки защёлки адреса и дешифратора.
