wwwcont/mpei-mps-kp/students/a09_drugovskaya_em/pz/pz2.md

<!-- Текст студента для ПЗ2. Каждый раздел начинается строкой «## ид — название»: ид не менять.
     Строки «> ✍ …» — подсказки, в документ не попадают. Пиши под подсказкой обычными абзацами;
     markdown можно: **жирный**, *курсив*, списки через «- ». Пустой раздел → в документе жёлтое «ДОПИШИ».
     Файл можно пересоздать (make pz-init): написанный текст сохранится. -->

## p2.ide — Среда разработки и компилятор
> ✍ если работали в другой среде — впишите свою (название и версия, например «MCU 8051 IDE 1.4.9») (необязательно: без текста в документ идёт пересказ схемы)

## p2.alg — Алгоритм программы в целом
> ✍ опиши основной цикл: что делается после сброса (инициализация), что крутится в основном цикле и какие действия выполняются в прерываниях (клавиатура — INT0, X2 — INT1, таймеры). 1–2 абзаца, со ссылками на рисунки ниже.

После сброса программа один раз проходит инициализацию (рисунок 1): указатель стека ставится на 07h, сигналом CS_EN = 1 включается дешифратор адреса, стробы Y1 и Y2 переводятся в пассивную единицу, все три столбца клавиатуры опускаются в ноль, индикатор гасится, буфер объявляется пустым (голова и хвост на 8000h, флаг пустоты взведён), оба таймера настраиваются в 16-разрядный режим и разрешаются прерывания. Основной цикл (рисунок 2) только следит за буфером: пока X1 не равно нулю и в буфере есть отсчёты, он берёт очередной отсчёт X2 по хвосту, считает Y2 = (12 + X1 + X2) mod 256 и выдаёт его со стробом; при X1 = 0 он один раз выдаёт нулевое Y2.

Всё, что приходит снаружи, обрабатывается в прерываниях. Нажатие клавиши даёт INT0: обработчик опрашивает матрицу 3×4 (рисунок 3) и по коду запоминает X1 и показывает цифру, запускает строб Y1 или очищает буфер (рисунок 4). Строб X2 от внешнего устройства приходит на INT1 по спаду; отсчёт к этому моменту ещё только записывается правым портом в ячейку обмена 9FFFh (ОЗУ фиксирует его по фронту строба), поэтому обработчик сначала ждёт, пока P3.3 вернётся в 1, затем читает ячейку левым портом и кладёт отсчёт в кольцо (рисунки 5 и 6). Длительности отсчитывают таймеры: Timer0 с тиком 5 мс заканчивает строб Y1 через 43 тика и гасит индикатор через 486 тиков (рисунок 10), Timer1 одной загрузкой отмеряет строб Y2 (рисунок 13).

## flow.01-init — Пояснение к рисунку 1
> ✍ своё пояснение к рисунку 1 («Инициализация МПС и основная программа»): что делает алгоритм по шагам и почему так (3–6 предложений) (необязательно: без текста в документ идёт пересказ схемы)

## flow.02-main — Пояснение к рисунку 2
> ✍ своё пояснение к рисунку 2 («Основной цикл программы»): что делает алгоритм по шагам и почему так (3–6 предложений) (необязательно: без текста в документ идёт пересказ схемы)

## flow.03-kbscan — Пояснение к рисунку 3
> ✍ своё пояснение к рисунку 3 («Опрос клавиатуры (обработчик INT0)»): что делает алгоритм по шагам и почему так (3–6 предложений) (необязательно: без текста в документ идёт пересказ схемы)

Процедура KbScan опускает в ноль по очереди один из трёх столбцов и каждый раз читает строки. Старшие биты прочитанного байта не подключены, поэтому они отбрасываются, а оставшиеся четыре инвертируются, чтобы единица означала замкнутую строку. Каждую замкнутую строку процедура считает и запоминает номер клавиши как «строка × 3 + столбец». После перебора все столбцы снова опускаются, иначе следующее нажатие не даст прерывания, и сбрасывается флаг IE0, который взвёлся, пока столбцы переключались. Если найдено ровно одно нажатие, номер переводится в код по таблице KeyTab, иначе возвращается FFh.

## flow.04-keys — Пояснение к рисунку 4
> ✍ своё пояснение к рисунку 4 («Обработчик прерывания INT0: реакция на клавишу»): что делает алгоритм по шагам и почему так (3–6 предложений) (необязательно: без текста в документ идёт пересказ схемы)

## flow.05-bufwrite — Пояснение к рисунку 5
> ✍ своё пояснение к рисунку 5 («Запись отсчёта в кольцевой буфер»): что делает алгоритм по шагам и почему так (3–6 предложений) (необязательно: без текста в документ идёт пересказ схемы)

Процедура BufWrite сначала проверяет, не заполнено ли кольцо: это случай, когда голова совпала с хвостом, а флаг пустоты сброшен. Тогда хвост сдвигается на одну ячейку вперёд, самый старый отсчёт пропадает и ставится флаг переполнения — то есть кольцо вмещает все 1530 отсчётов (политика V). Затем отсчёт записывается левым портом по адресу головы, голова сдвигается, флаг пустоты сбрасывается. Переход на следующую ячейку вынесен в отдельную процедуру PtrStep: она увеличивает адрес и после 85F9h возвращает его на 8000h, сравнивая оба байта.

## flow.05a-x2isr — Пояснение к рисунку 6
> ✍ своё пояснение к рисунку 6 («Обработчик прерывания INT1: приём отсчёта X2 от внешнего устройства»): что делает алгоритм по шагам и почему так (3–6 предложений) (необязательно: без текста в документ идёт пересказ схемы)

Обработчик INT1 вызывается по спаду строба X2, но правый порт IDT7005 запоминает байт только по его фронту, поэтому первым делом обработчик крутится, пока на P3.3 снова не появится единица. После этого в ячейке обмена 9FFFh гарантированно лежит новый отсчёт, и обработчик читает его левым портом командой movx. Прочитанный байт передаётся процедуре записи в кольцо (рисунок 5), которая сама ведёт голову, хвост и флаги. Регистры A, PSW и DPTR сохраняются в стеке, потому что прерывание может прийти в любой точке основной программы.

## flow.06-bufread — Пояснение к рисунку 7
> ✍ своё пояснение к рисунку 7 («Чтение отсчёта из кольцевого буфера»): что делает алгоритм по шагам и почему так (3–6 предложений) (необязательно: без текста в документ идёт пересказ схемы)

## flow.07-bufclear — Пояснение к рисунку 8
> ✍ своё пояснение к рисунку 8 («Очистка кольцевого буфера (клавиша «Сброс»)»): что делает алгоритм по шагам и почему так (3–6 предложений) (необязательно: без текста в документ идёт пересказ схемы)

## flow.08-show — Пояснение к рисунку 9
> ✍ своё пояснение к рисунку 9 («Вывод символа на индикатор»): что делает алгоритм по шагам и почему так (3–6 предложений) (необязательно: без текста в документ идёт пересказ схемы)

Процедура Show получает код символа в аккумуляторе. Коды 0–10 переводятся по таблице SegTab сразу в коды сегментов для индикатора с общим анодом (сегмент горит при нуле) и записываются в регистр индикатора. После этого отсчёт T3 начинается заново: Timer0 останавливается, счётчик тиков получает значение 486 (2430 мс по 5 мс), таймер загружается на первый тик и запускается — поэтому новый символ всегда горит полное T3. Для кодов 11 и больше индикатор сразу гасится, а таймер останавливается, так как ждать нечего.

## flow.09-t0 — Пояснение к рисунку 10
> ✍ своё пояснение к рисунку 10 («Обработчик прерывания Timer0: отсчёт T1 и T3»): что делает алгоритм по шагам и почему так (3–6 предложений) (необязательно: без текста в документ идёт пересказ схемы)

Таймер 0 работает в 16-разрядном режиме и сам не перезагружается, поэтому обработчик на каждом тике заново загружает его на 5 мс. К загружаемому значению прибавляется то, что таймер успел насчитать после переполнения, плюс семь циклов, пока он стоит, — так задержка входа в прерывание не накапливается за 486 тиков. Затем уменьшается 16-разрядный счётчик тиков, и когда он доходит до нуля, таймер останавливается и индикатор гаснет (в полной системе тот же таймер заканчивает и строб Y1).

## flow.10-y1 — Пояснение к рисунку 11
> ✍ своё пояснение к рисунку 11 («Начало строба Y1»): что делает алгоритм по шагам и почему так (3–6 предложений) (необязательно: без текста в документ идёт пересказ схемы)

## flow.11-y2 — Пояснение к рисунку 12
> ✍ своё пояснение к рисунку 12 («Расчёт и выдача сигнала Y2»): что делает алгоритм по шагам и почему так (3–6 предложений) (необязательно: без текста в документ идёт пересказ схемы)

## flow.12-t1 — Пояснение к рисунку 13
> ✍ своё пояснение к рисунку 13 («Обработчик прерывания Timer1: конец строба Y2»): что делает алгоритм по шагам и почему так (3–6 предложений) (необязательно: без текста в документ идёт пересказ схемы)

## p2.errors — Коды ошибок
> ✍ проверь таблицу кодов ошибок выше: оставь те, что обрабатывает твоя программа, и одним-двумя предложениями опиши реакцию на ошибку (или напиши «таблица соответствует программе»).

Таблица описывает реакцию полной системы. В написанных программах источники ошибок такие: процедура опроса клавиатуры возвращает FFh и при нескольких нажатых клавишах, и при отсутствии нажатия (в полной системе обработчик INT0 в ответ на FFh выводит код ошибки на индикатор, рисунок 4), а процедура записи в буфер при затирании непрочитанного отсчёта ставит флаг переполнения 21h.4 (код «3.»). Код «4.» относится к стробу Y1, который в трёх программах варианта не реализуется.
