wwwcont/mpei-mps-kp/students/ae21_sudbinin_na/pz/pz1.md

<!-- Текст студента для ПЗ1. Каждый раздел начинается строкой «## ид — название»: ид не менять.
     Строки «> ✍ …» — подсказки, в документ не попадают. Пиши под подсказкой обычными абзацами;
     markdown можно: **жирный**, *курсив*, списки через «- ». Пустой раздел → в документе жёлтое «ДОПИШИ».
     Файл можно пересоздать (make pz-init): написанный текст сохранится. -->

## p1.intro — Введение: своими словами
> ✍ одним абзацем — что делает твоя система и чем вариант отличается (клавиатура, индикатор, сигналы Y). Можно удалить подсказку, если введение устраивает.
Разрабатываемая система на микроконтроллере AT89S53 принимает от внешнего устройства поток восьмиразрядных отсчётов X2, складывает их в кольцевой буфер на двухпортовой памяти IDT7005, а с пульта получает цифру X1 и по ним выдаёт на выходной регистр сигнал Y2 = (21 + 11 + X1 + X2) mod 256 со стробом длительностью 1751 мкс на выводе P1.5. Кроме этого, клавишей «Тест» формируется строб Y1 на P1.4 длительностью 313 мс, а нажатый символ держится на индикаторе 2,745 с. Особенности моего варианта (Аэ-21, M = 11): клавиатура 3×4 (три столбца, четыре строки), индикатор с общим катодом, буфер на 1910 байт выбирается выходом Y7 дешифратора 74HC138, регистр Y2 — выходом Y2, индикатор — Y1, клавиатура — Y3.

## p1.buffer — Механизм обмена через буфер
> ✍ опиши своими словами, как внешнее устройство записывает X2 и как МК читает буфер (кто выставляет адрес, какой строб, какое прерывание, кто двигает «голову» и «хвост»). 3–5 предложений.
Порты IDT7005 у меня разделены: левый целиком подключён к микроконтроллеру (A0–A12, D0–D7, CE от выхода Y7 дешифратора, OE от RD, R/W от WR), а правый целиком выведен на отдельный разъём доступа к буферу, где адрес, данные и строб записи R/W выставляет само внешнее устройство (CE и OE правого порта постоянно активны). Очередной отсчёт X2 внешнее устройство записывает правым портом в ячейку обмена 0FFFFh, которая лежит вне кольца 0E000h–0E775h, и тот же строб записи приходит на вход INT1. Прерывание срабатывает по спаду строба, а память фиксирует байт только по его фронту, поэтому обработчик INT1 сначала ждёт, пока на P3.3 снова появится единица, и лишь потом читает ячейку обмена левым портом (movx A,@DPTR по RD). Прочитанный отсчёт обработчик передаёт процедуре записи, которая кладёт его в ячейку «головы», сдвигает «голову» (после 0E775h — на 0E000h) и снимает флаг пустоты; при заполненном кольце она же сдвигает «хвост», выбрасывая самый старый отсчёт, и ставит флаг переполнения. Указатели и флаги целиком ведёт МК: при расчёте Y2 процедура чтения берёт отсчёт из ячейки «хвоста» тем же левым портом и сдвигает «хвост», а результат уходит в регистр Y2.

## p1.timing — Вывод по временам IDT7005
> ✍ свой вывод по сравнению времён (2–4 предложения) (необязательно: без текста в документ идёт пересказ схемы)
