wwwcont/mpei-mps-kp/А-09-23/3 Друговская Е.М./СХЕМА-1/schematic.png

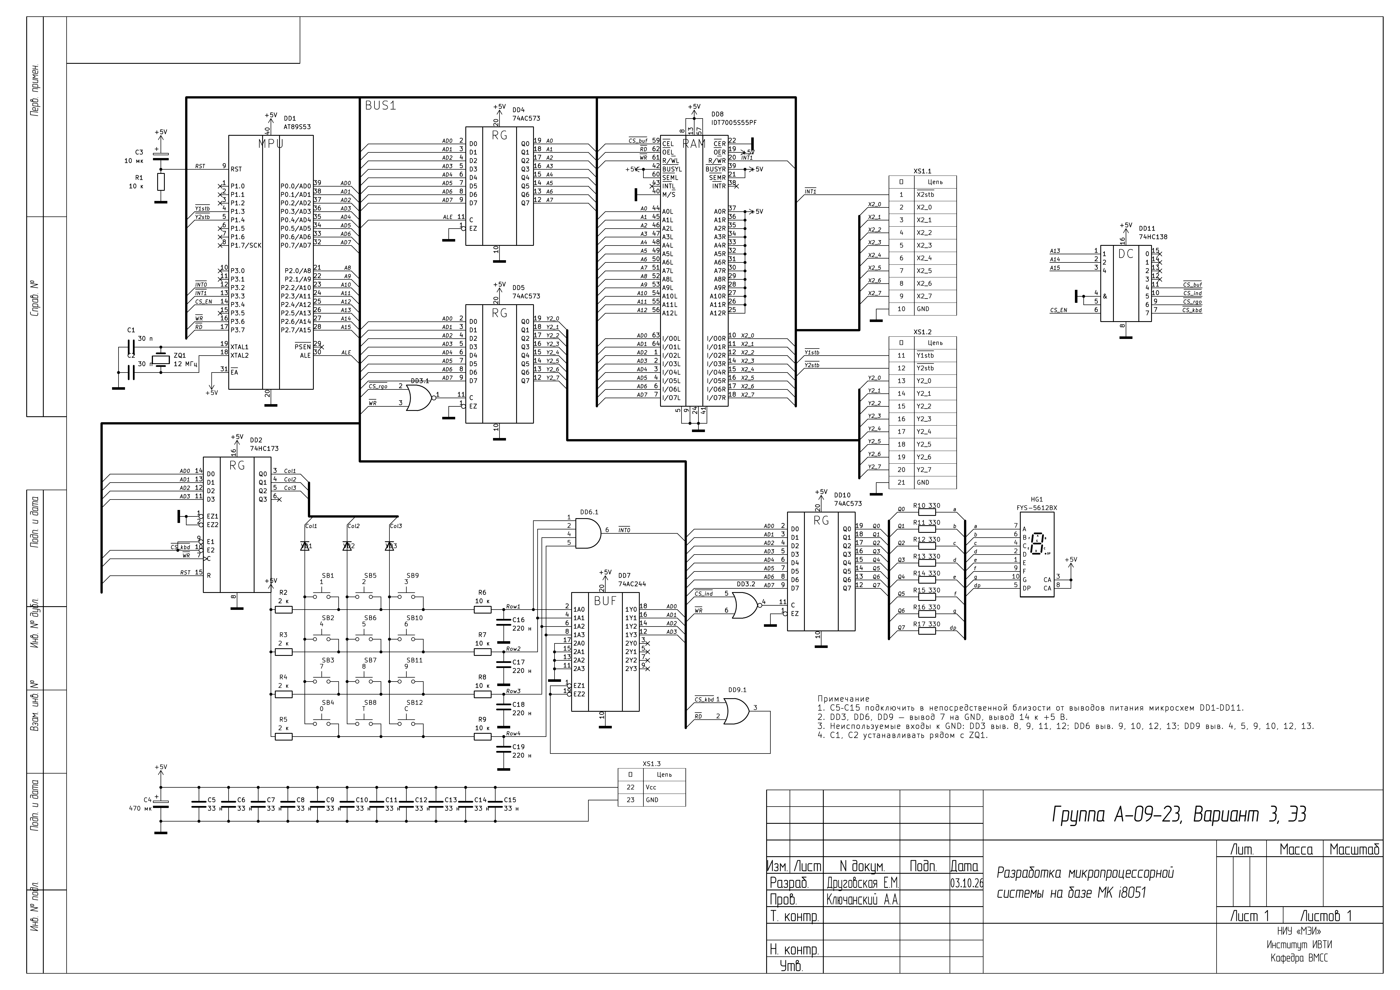
А-09-23/3 Друговская Е.М./СХЕМА-1/schematic.png
