wwwcont/mpei-mps-kp/А-12-23/8 Казарин А.А./СХЕМА-1/perechen-2.png

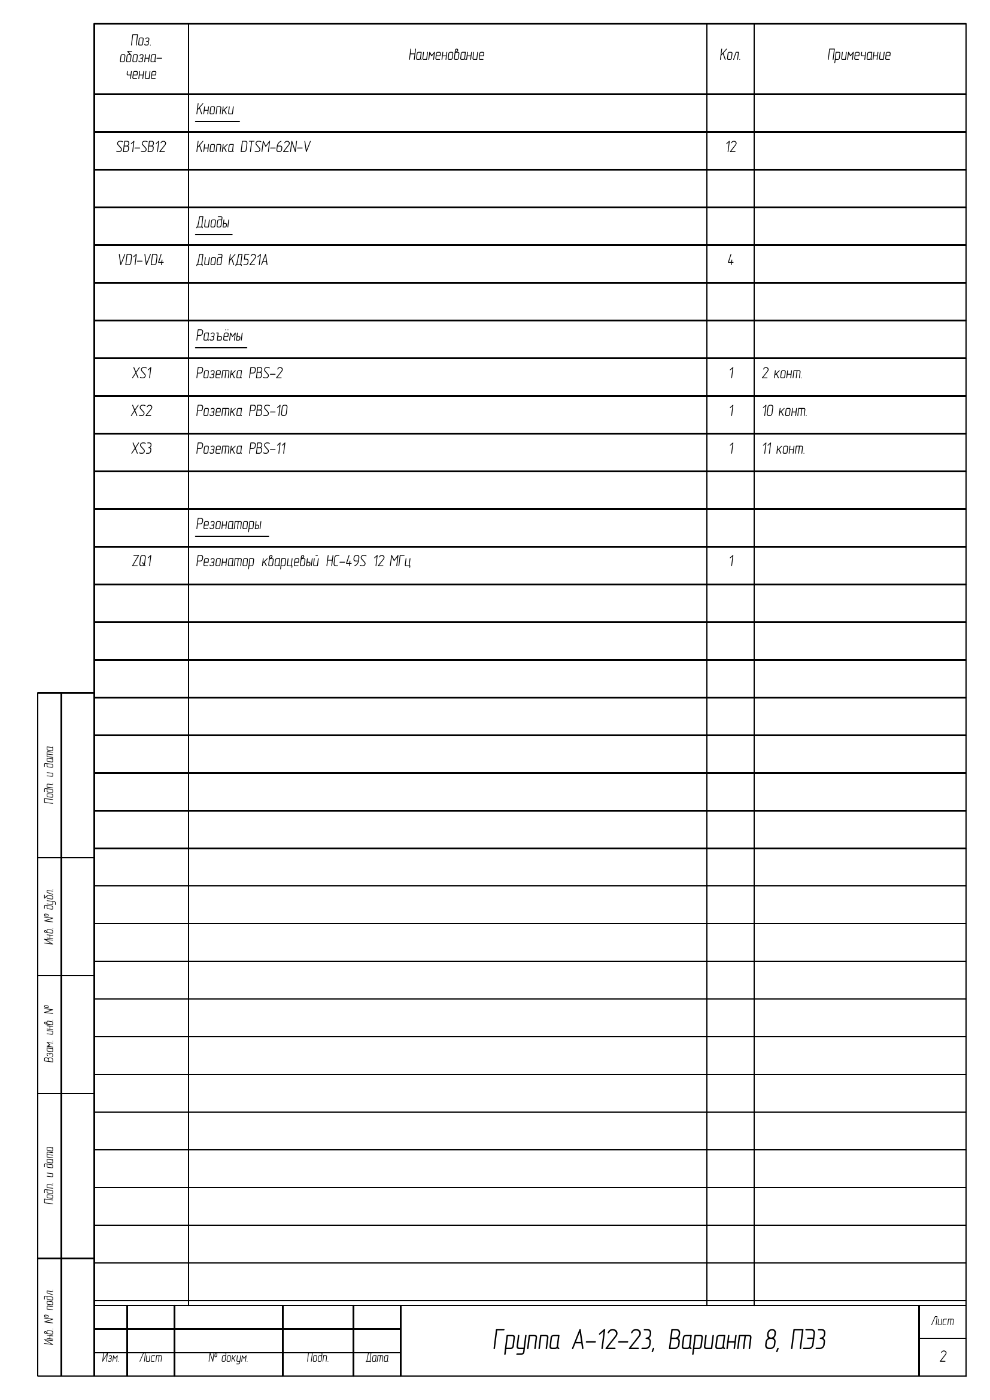
А-12-23/8 Казарин А.А./СХЕМА-1/perechen-2.png
