wwwcont/mpei-mps-kp/А-12-23/8 Казарин А.А./СХЕМА-1/schematic.kicad_sch

## KiCad design А-12-23/8 Казарин А.А./СХЕМА-1/schematic.kicad_sch (2026-10-03)

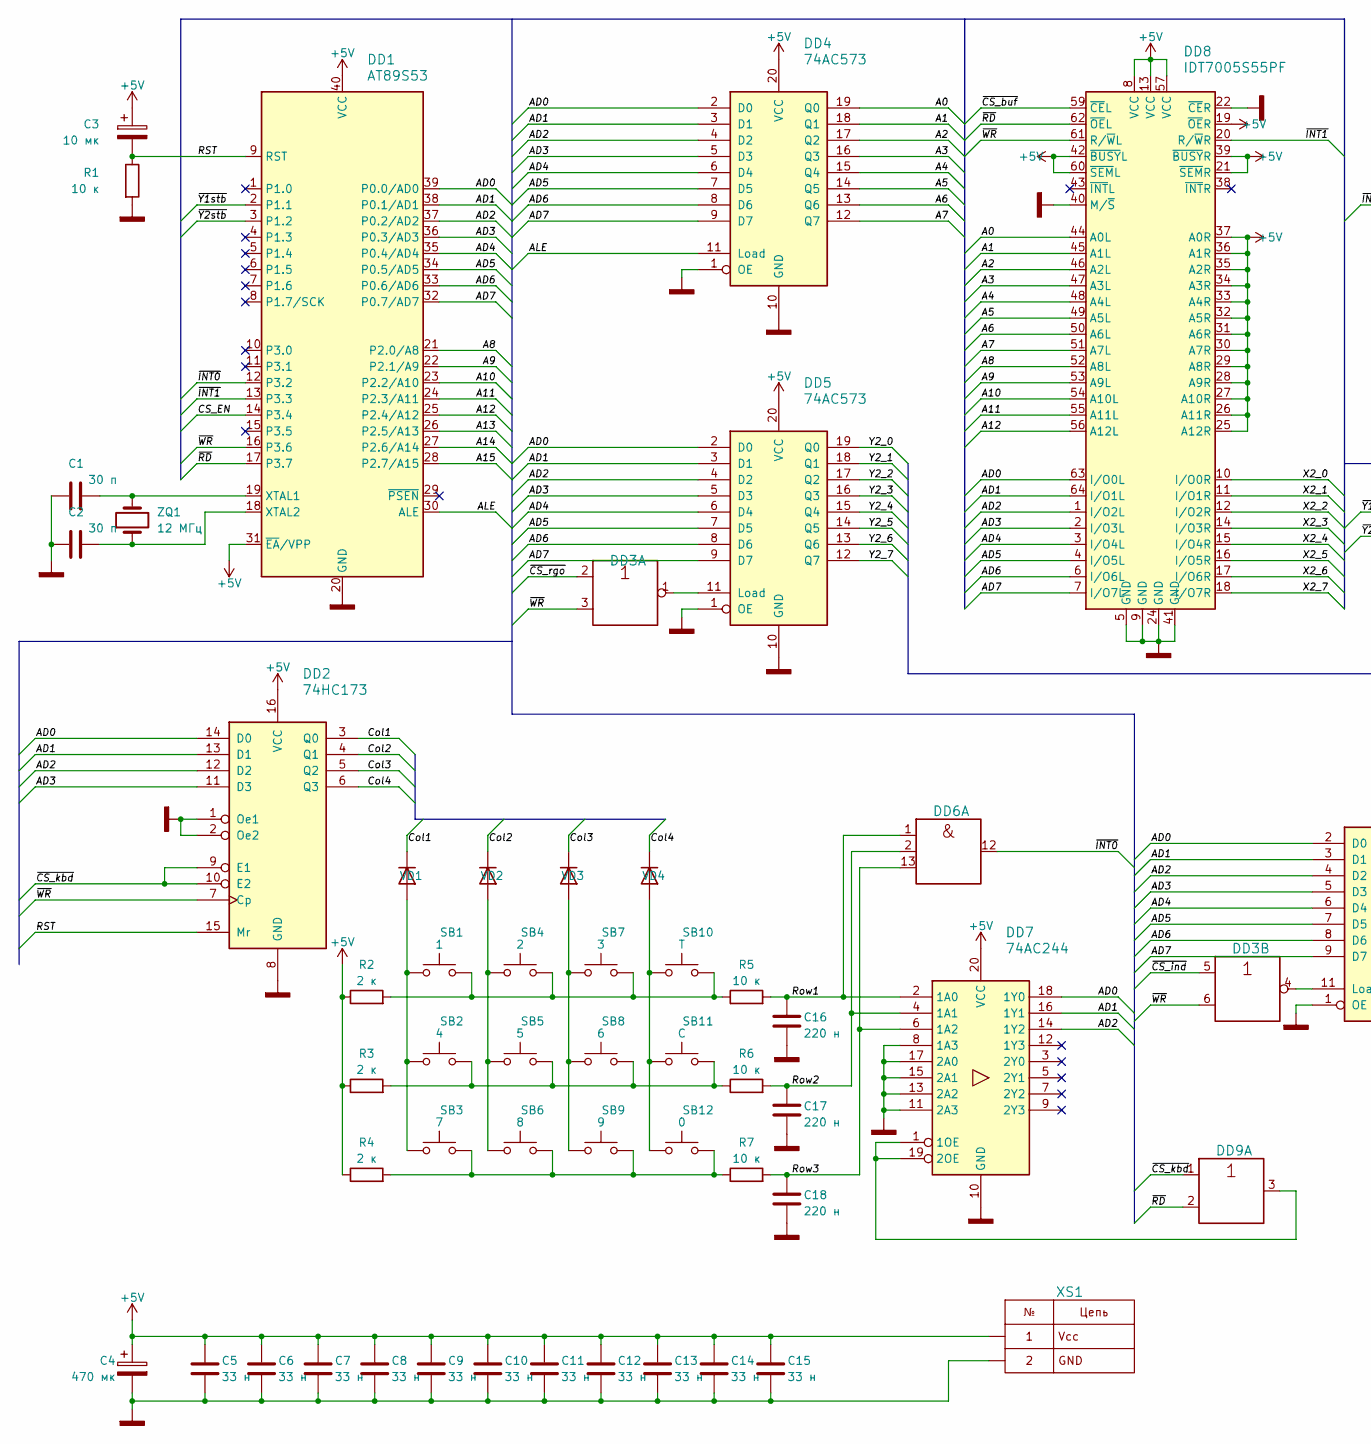
[picture p85: schematic schematic.kicad_sch, part in row 1, column 1]

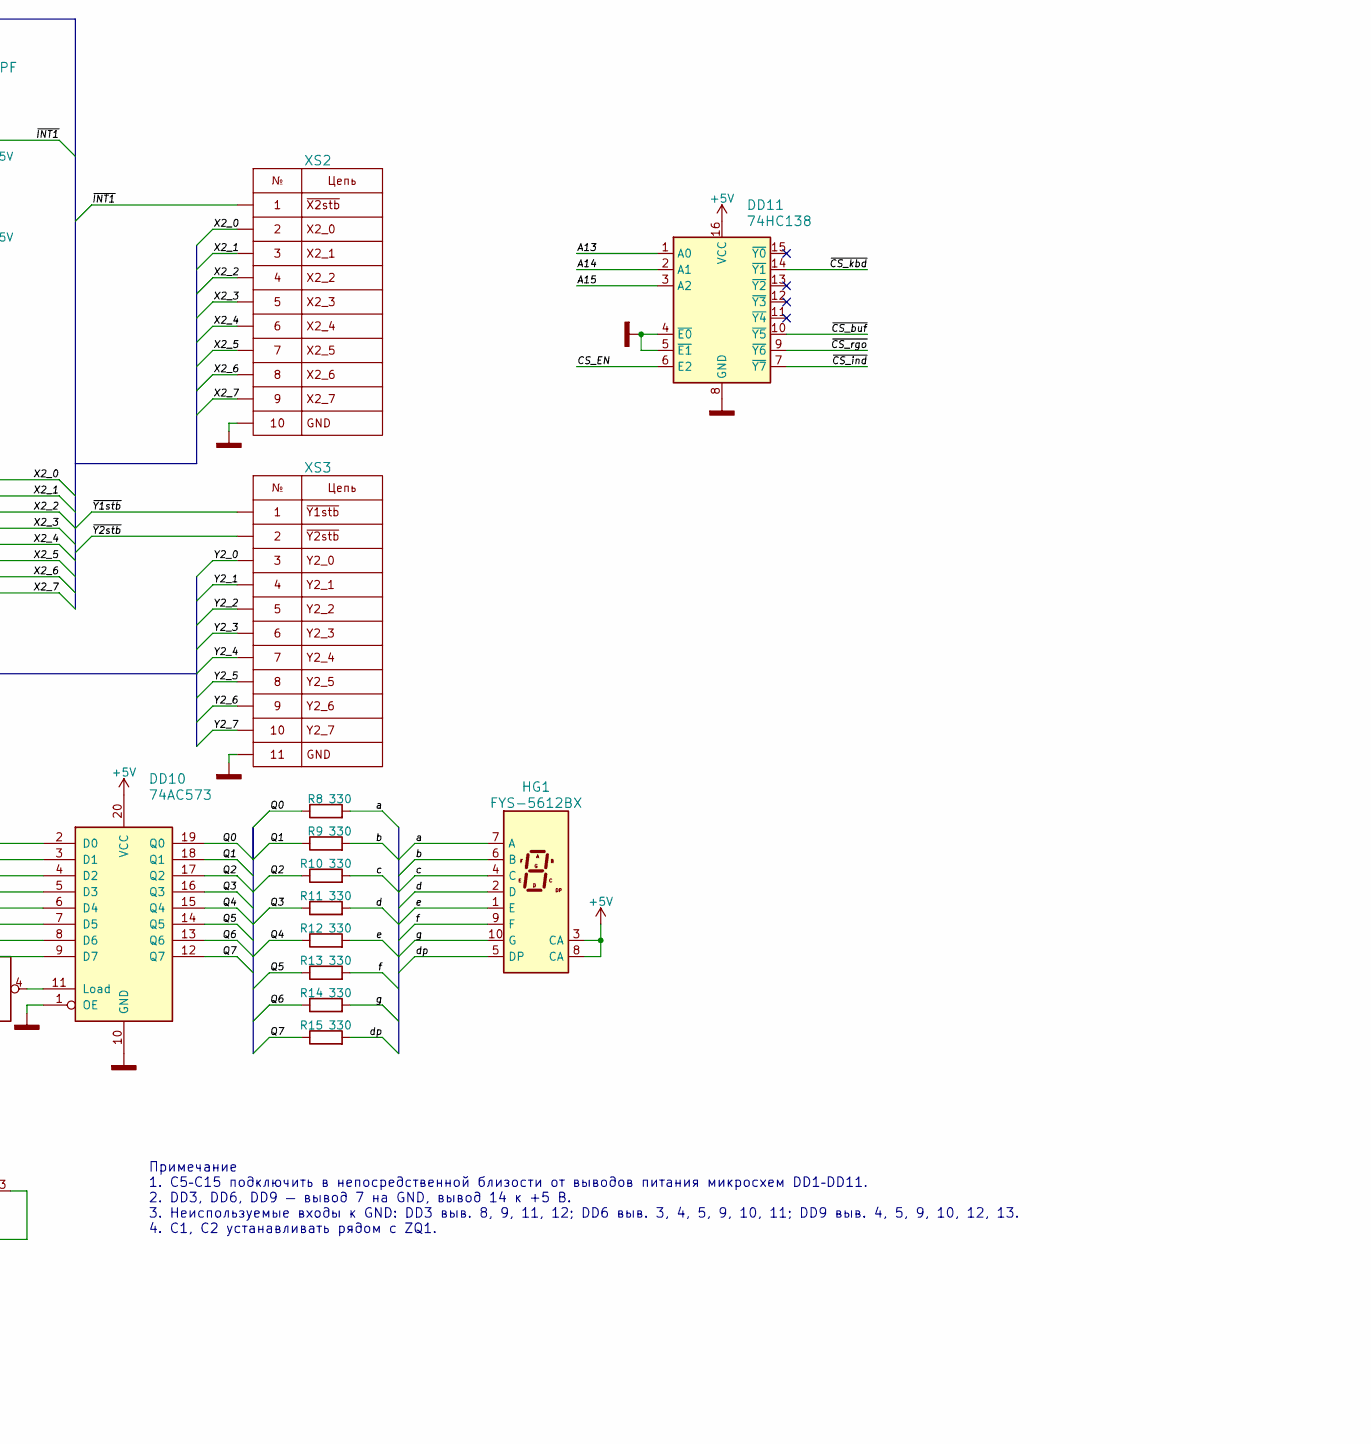
[picture p86: schematic schematic.kicad_sch, part in row 1, column 2]

Parts:
C1, C2: 30 п
C3: 10 мк
C4: 470 мк
C5, C6, C7, C8, C9, C10, C11, C12, C13, C14, C15: 33 н
C16, C17, C18: 220 н
DD1: AT89S53; DIP-40_W15.24mm
DD2: 74HC173
DD3: 74HC02
DD4, DD5, DD10: 74AC573
DD6: 74HC11
DD7: 74AC244
DD8: IDT7005S55PF; TQFP-64_14x14mm_P0.8mm
DD9: 74HC32
DD11: 74HC138
HG1: FYS-5612BX; KCSC02-105
R1, R5, R6, R7: 10 к
R2, R3, R4: 2 к
R8, R9, R10, R11, R12, R13, R14, R15: 330
SB1: 1
SB2: 4
SB3: 7
SB4: 2
SB5: 5
SB6: 8
SB7: 3
SB8: 6
SB9: 9
SB10: Т
SB11: С
SB12: 0
VD1, VD2, VD3, VD4: КД521А
XS1, XS2, XS3: (no value)
ZQ1: 12 МГц

Connections:
+5V: C3.1, C4.1, C5.1, C6.1, C7.1, C8.1, C9.1, C10.1, C11.1, C12.1, C13.1, C14.1, C15.1, DD1.31 (~EA/VPP), DD1.40 (VCC), DD2.16 (VCC), DD4.20 (VCC), DD5.20 (VCC), DD7.20 (VCC), DD8.8 (VCC), DD8.13 (VCC), DD8.19 (~OER), DD8.21 (~SEMR), DD8.25 (A12R), DD8.26 (A11R), DD8.27 (A10R), DD8.28 (A9R), DD8.29 (A8R), DD8.30 (A7R), DD8.31 (A6R), DD8.32 (A5R), DD8.33 (A4R), DD8.34 (A3R), DD8.35 (A2R), DD8.36 (A1R), DD8.37 (A0R), DD8.39 (~BUSYR), DD8.42 (~BUSYL), DD8.57 (VCC), DD8.60 (~SEML), DD10.20 (VCC), DD11.16 (VCC), HG1.3 (CA), HG1.8 (CA), R2.1, R3.1, R4.1, XS1.1 (Vcc)
A0: DD4.19 (Q0), DD8.44 (A0L)
A1: DD4.18 (Q1), DD8.45 (A1L)
A2: DD4.17 (Q2), DD8.46 (A2L)
A3: DD4.16 (Q3), DD8.47 (A3L)
A4: DD4.15 (Q4), DD8.48 (A4L)
A5: DD4.14 (Q5), DD8.49 (A5L)
A6: DD4.13 (Q6), DD8.50 (A6L)
A7: DD4.12 (Q7), DD8.51 (A7L)
A8: DD1.21 (P2.0/A8), DD8.52 (A8L)
A9: DD1.22 (P2.1/A9), DD8.53 (A9L)
A10: DD1.23 (P2.2/A10), DD8.54 (A10L)
A11: DD1.24 (P2.3/A11), DD8.55 (A11L)
A12: DD1.25 (P2.4/A12), DD8.56 (A12L)
A13: DD1.26 (P2.5/A13), DD11.1 (A0)
A14: DD1.27 (P2.6/A14), DD11.2 (A1)
A15: DD1.28 (P2.7/A15), DD11.3 (A2)
AD0: DD1.39 (P0.0/AD0), DD2.14 (D0), DD4.2 (D0), DD5.2 (D0), DD7.18 (1Y0), DD8.63 (I/O0L), DD10.2 (D0)
AD1: DD1.38 (P0.1/AD1), DD2.13 (D1), DD4.3 (D1), DD5.3 (D1), DD7.16 (1Y1), DD8.64 (I/O1L), DD10.3 (D1)
AD2: DD1.37 (P0.2/AD2), DD2.12 (D2), DD4.4 (D2), DD5.4 (D2), DD7.14 (1Y2), DD8.1 (I/O2L), DD10.4 (D2)
AD3: DD1.36 (P0.3/AD3), DD2.11 (D3), DD4.5 (D3), DD5.5 (D3), DD8.2 (I/O3L), DD10.5 (D3)
AD4: DD1.35 (P0.4/AD4), DD4.6 (D4), DD5.6 (D4), DD8.3 (I/O4L), DD10.6 (D4)
AD5: DD1.34 (P0.5/AD5), DD4.7 (D5), DD5.7 (D5), DD8.4 (I/O5L), DD10.7 (D5)
AD6: DD1.33 (P0.6/AD6), DD4.8 (D6), DD5.8 (D6), DD8.6 (I/O6L), DD10.8 (D6)
AD7: DD1.32 (P0.7/AD7), DD4.9 (D7), DD5.9 (D7), DD8.7 (I/O7L), DD10.9 (D7)
ALE: DD1.30 (ALE), DD4.11 (Load)
CS_EN: DD1.14 (P3.4), DD11.6 (E2)
Col1: DD2.3 (Q0), VD1.1 (K)
Col2: DD2.4 (Q1), VD2.1 (K)
Col3: DD2.5 (Q2), VD3.1 (K)
Col4: DD2.6 (Q3), VD4.1 (K)
GND: C1.1, C2.1, C4.2, C5.2, C6.2, C7.2, C8.2, C9.2, C10.2, C11.2, C12.2, C13.2, C14.2, C15.2, C16.2, C17.2, C18.2, DD1.20 (GND), DD2.1 (Oe1), DD2.2 (Oe2), DD2.8 (GND), DD4.1 (OE), DD4.10 (GND), DD5.1 (OE), DD5.10 (GND), DD7.8 (1A3), DD7.10 (GND), DD7.11 (2A3), DD7.13 (2A2), DD7.15 (2A1), DD7.17 (2A0), DD8.5 (GND), DD8.9 (GND), DD8.22 (~CER), DD8.24 (GND), DD8.40 (M/~S), DD8.41 (GND), DD10.1 (OE), DD10.10 (GND), DD11.4 (~E0), DD11.5 (~E1), DD11.8 (GND), R1.2, XS1.2 (GND), XS2.10 (GND), XS3.11 (GND)
unnamed: C1.2, DD1.19 (XTAL1), ZQ1.2
unnamed: C2.2, DD1.18 (XTAL2), ZQ1.1
unnamed: DD3.1, DD5.11 (Load)
unnamed: DD7.1 (1OE), DD7.19 (2OE), DD9.3
unnamed: DD3.4, DD10.11 (Load)
unnamed: R2.2, R5.1, SB1.2, SB4.2, SB7.2, SB10.2
unnamed: R3.2, R6.1, SB2.2, SB5.2, SB8.2, SB11.2
unnamed: R4.2, R7.1, SB3.2, SB6.2, SB9.2, SB12.2
unnamed: SB1.1, SB2.1, SB3.1, VD1.2 (A)
unnamed: SB4.1, SB5.1, SB6.1, VD2.2 (A)
unnamed: SB7.1, SB8.1, SB9.1, VD3.2 (A)
unnamed: SB10.1, SB11.1, SB12.1, VD4.2 (A)
Q0: DD10.19 (Q0), R8.1
Q1: DD10.18 (Q1), R9.1
Q2: DD10.17 (Q2), R10.1
Q3: DD10.16 (Q3), R11.1
Q4: DD10.15 (Q4), R12.1
Q5: DD10.14 (Q5), R13.1
Q6: DD10.13 (Q6), R14.1
Q7: DD10.12 (Q7), R15.1
RST: C3.2, DD1.9 (RST), DD2.15 (Mr), R1.1
Row1: C16.1, DD6.1, DD7.2 (1A0), R5.2
Row2: C17.1, DD6.2, DD7.4 (1A1), R6.2
Row3: C18.1, DD6.13, DD7.6 (1A2), R7.2
X2_0: DD8.10 (I/O0R), XS2.2 (X2_0)
X2_1: DD8.11 (I/O1R), XS2.3 (X2_1)
X2_2: DD8.12 (I/O2R), XS2.4 (X2_2)
X2_3: DD8.14 (I/O3R), XS2.5 (X2_3)
X2_4: DD8.15 (I/O4R), XS2.6 (X2_4)
X2_5: DD8.16 (I/O5R), XS2.7 (X2_5)
X2_6: DD8.17 (I/O6R), XS2.8 (X2_6)
X2_7: DD8.18 (I/O7R), XS2.9 (X2_7)
Y2_0: DD5.19 (Q0), XS3.3 (Y2_0)
Y2_1: DD5.18 (Q1), XS3.4 (Y2_1)
Y2_2: DD5.17 (Q2), XS3.5 (Y2_2)
Y2_3: DD5.16 (Q3), XS3.6 (Y2_3)
Y2_4: DD5.15 (Q4), XS3.7 (Y2_4)
Y2_5: DD5.14 (Q5), XS3.8 (Y2_5)
Y2_6: DD5.13 (Q6), XS3.9 (Y2_6)
Y2_7: DD5.12 (Q7), XS3.10 (Y2_7)
a: HG1.7 (A), R8.2
b: HG1.6 (B), R9.2
c: HG1.4 (C), R10.2
d: HG1.2 (D), R11.2
dp: HG1.5 (DP), R15.2
e: HG1.1 (E), R12.2
f: HG1.9 (F), R13.2
g: HG1.10 (G), R14.2
~CS_buf: DD8.59 (~CEL), DD11.10 (~Y5)
~CS_ind: DD3.5, DD11.7 (~Y7)
~CS_kbd: DD2.9 (E1), DD2.10 (E2), DD9.1, DD11.14 (~Y1)
~CS_rgo: DD3.2, DD11.9 (~Y6)
~INT0: DD1.12 (P3.2), DD6.12
~INT1: DD1.13 (P3.3), DD8.20 (R/~WR), XS2.1 (~X2stb)
~RD: DD1.17 (P3.7), DD8.62 (~OEL), DD9.2
~WR: DD1.16 (P3.6), DD2.7 (Cp), DD3.3, DD3.6, DD8.61 (R/~WL)
~Y1stb: DD1.2 (P1.1), XS3.1 (~Y1stb)
~Y2stb: DD1.3 (P1.2), XS3.2 (~Y2stb)

Notes on the sheet:
Примечание 1. C5–C15 подключить в непосредственной близости от выводов питания микросхем DD1–DD11. 2. DD3, DD6, DD9 — вывод 7 на GND, вывод 14 к +5 В. 3. Неиспользуемые входы к GND: DD3 выв. 8, 9, 11, 12; DD6 выв. 3, 4, 5, 9, 10, 11; DD9 выв. 4, 5, 9, 10, 12, 13. 4. C1, C2 устанавливать рядом с ZQ1.
